joncox123/MotoButtons2/Case/MB2_Case.STEP

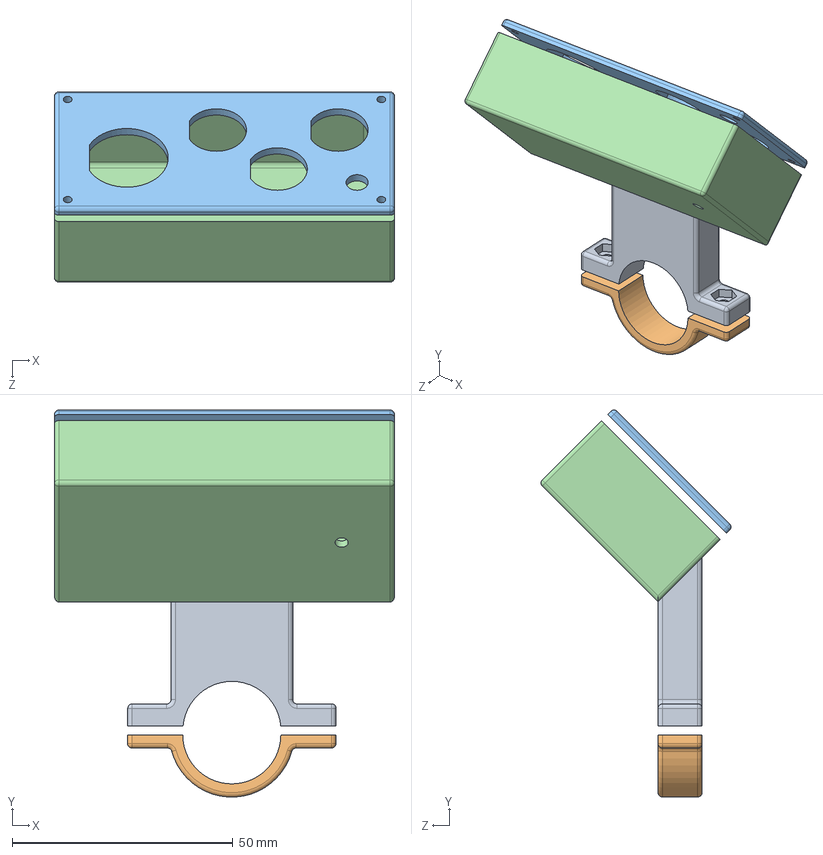
[picture p28: CAD file, 2024-03-28, an earlier design]
Case/MB2_Case.STEP
77.1 x 87.7 x 43.1 mm
hb_mount_top
hb_mount_bottom
case-bottom
